radimkeseg/osmoZis/img/JLCPCB_20190118_084337.jpg

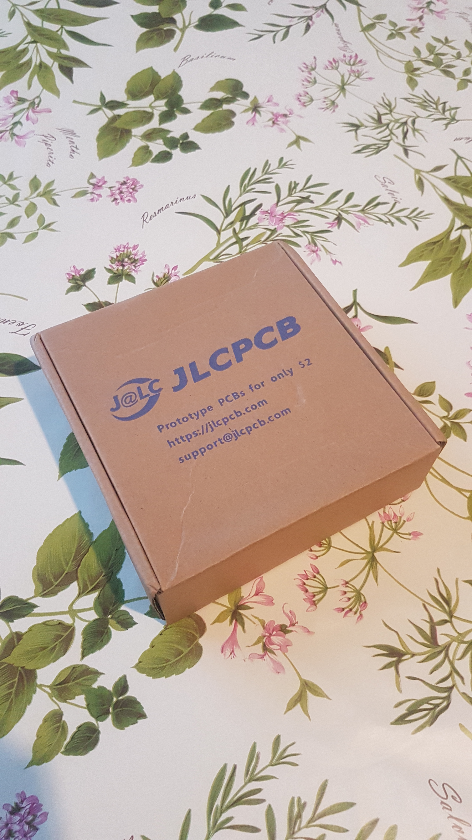
img/JLCPCB_20190118_084337.jpg
