radimkeseg/osmoZis/img/JLCPCB_20190118_084742.jpg

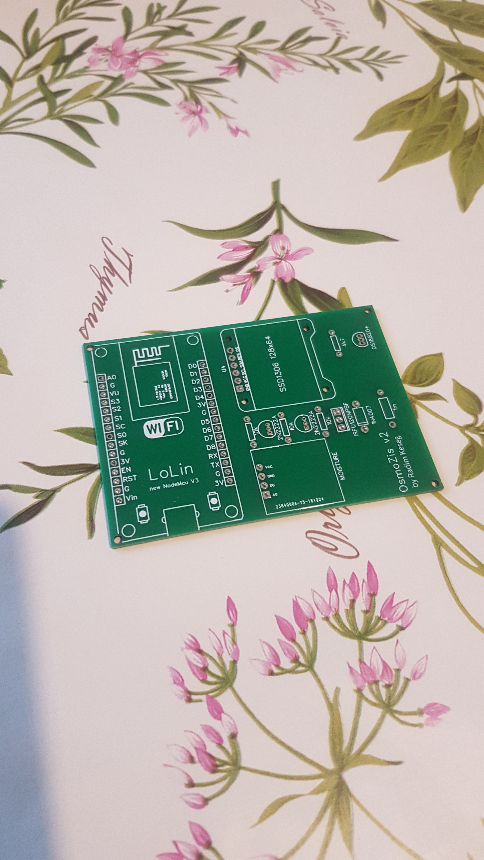
img/JLCPCB_20190118_084742.jpg
