radimkeseg/osmoZis/img/PCB TOP OsmoZis v2.jpg

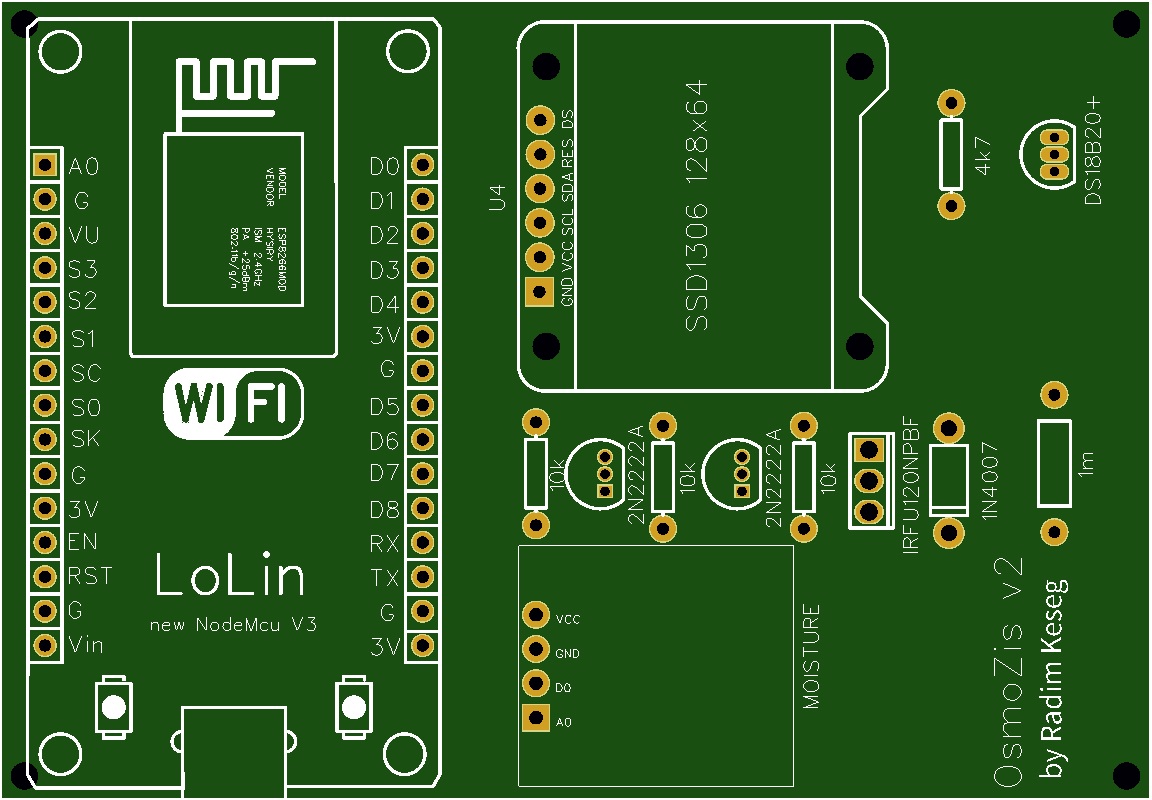
img/PCB TOP OsmoZis v2.jpg
